Sashabg1228/dread/documentation/documentation/images/robot-close.JPG

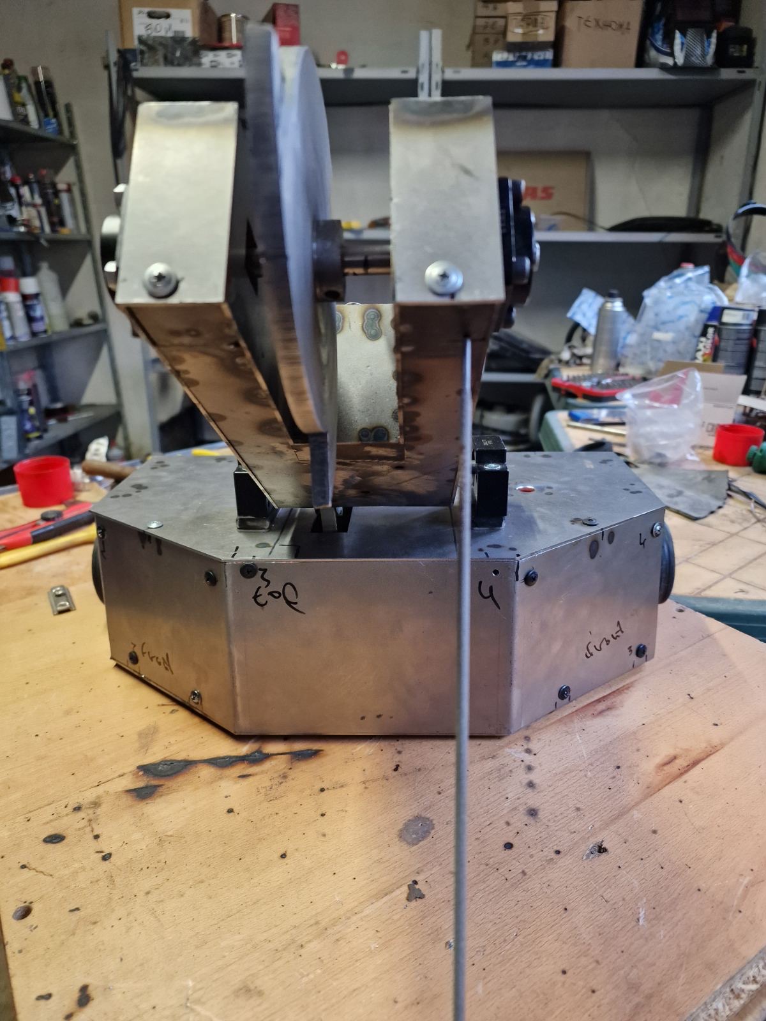
documentation/documentation/images/robot-close.JPG
