Sashabg1228/dread/documentation/documentation/images/robot-high.JPG

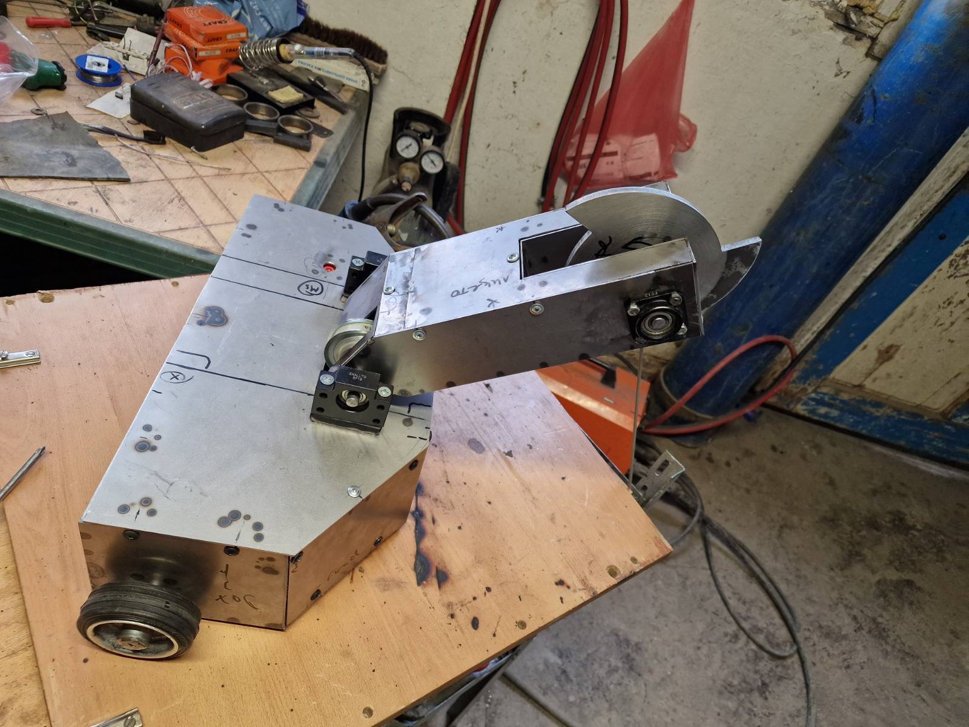
documentation/documentation/images/robot-high.JPG
