Sashabg1228/dread/documentation/documentation/images/robot-strange.JPG

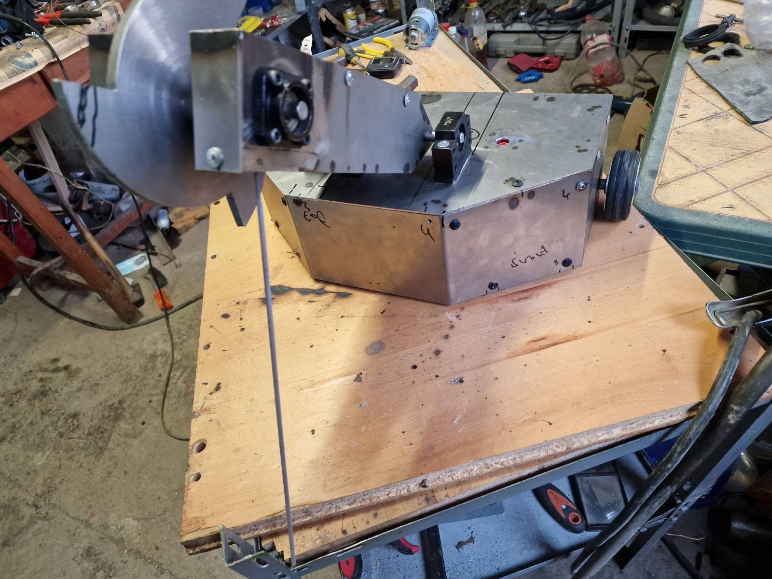
documentation/documentation/images/robot-strange.JPG
