Sashabg1228/dread/documentation/documentation/images/using-legs.png

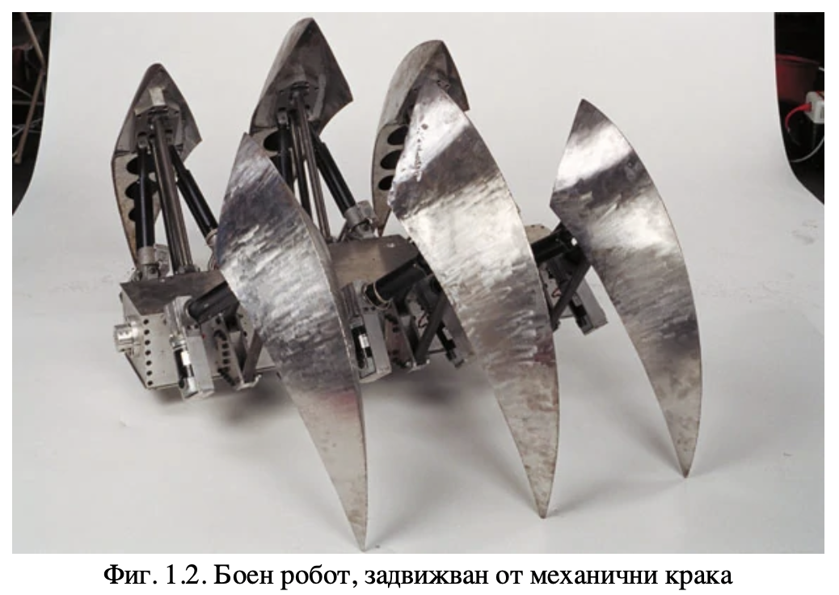
documentation/documentation/images/using-legs.png
