Sashabg1228/dread/documentation/documentation/images/wireless-comparison.png

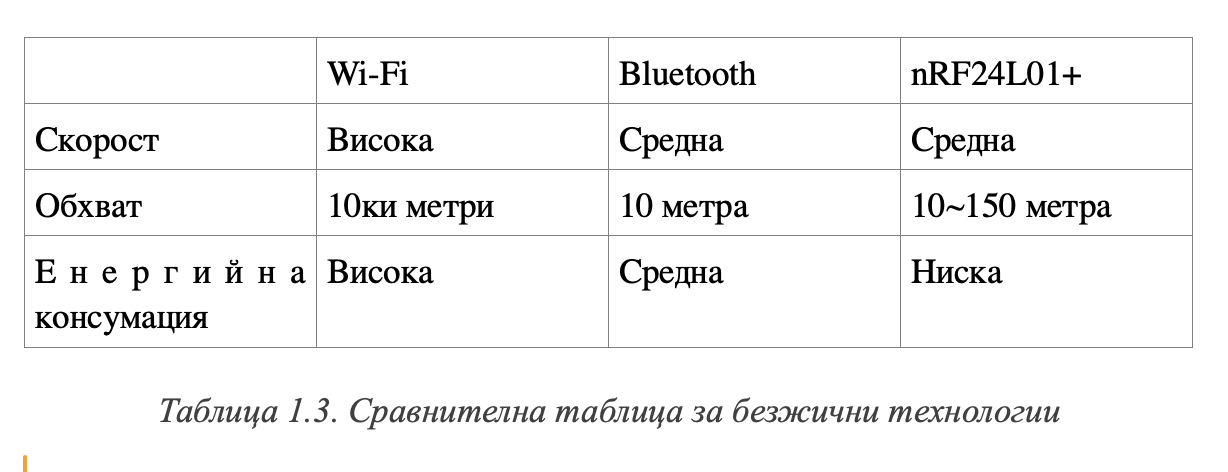
documentation/documentation/images/wireless-comparison.png
