Sashabg1228/dread/photos/IMG_7836.jpg

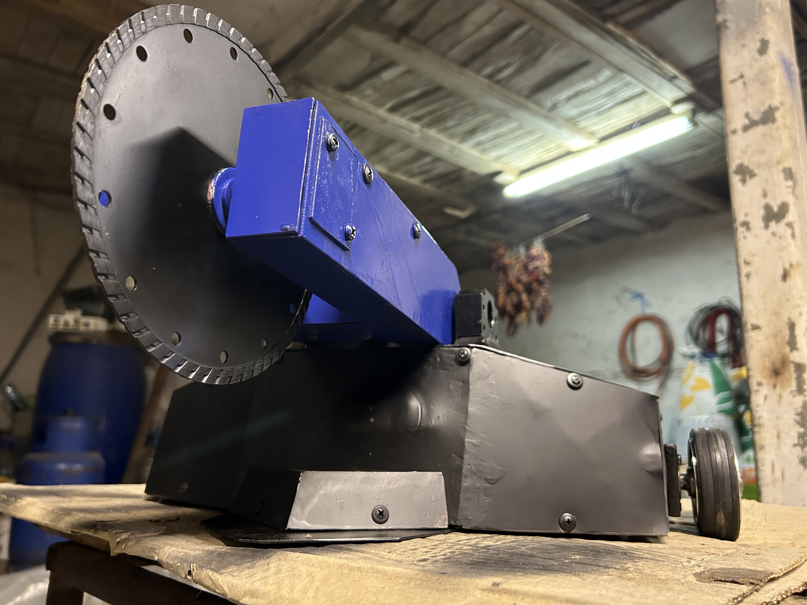
photos/IMG_7836.jpg
