Sashabg1228/dread/photos/IMG_7838.jpg

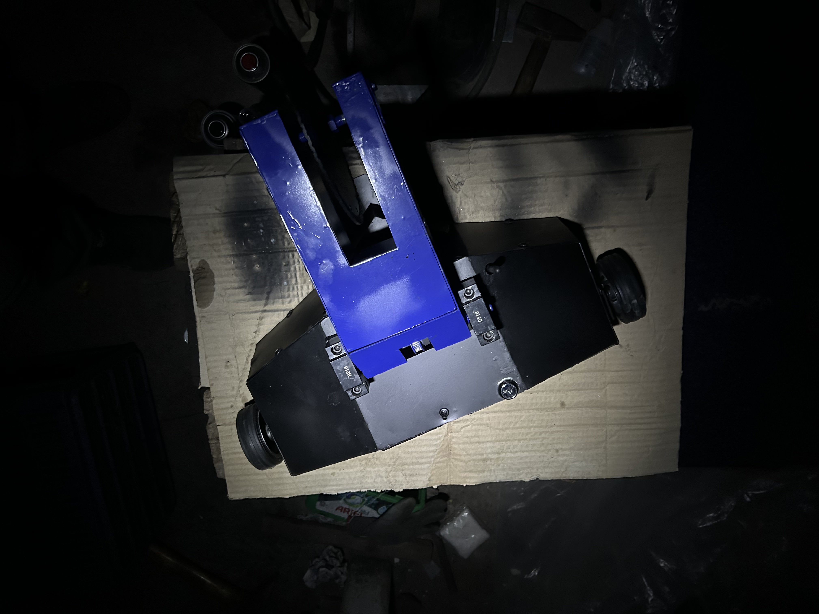
photos/IMG_7838.jpg
