Sashabg1228/dread/photos/IMG_7841.jpg

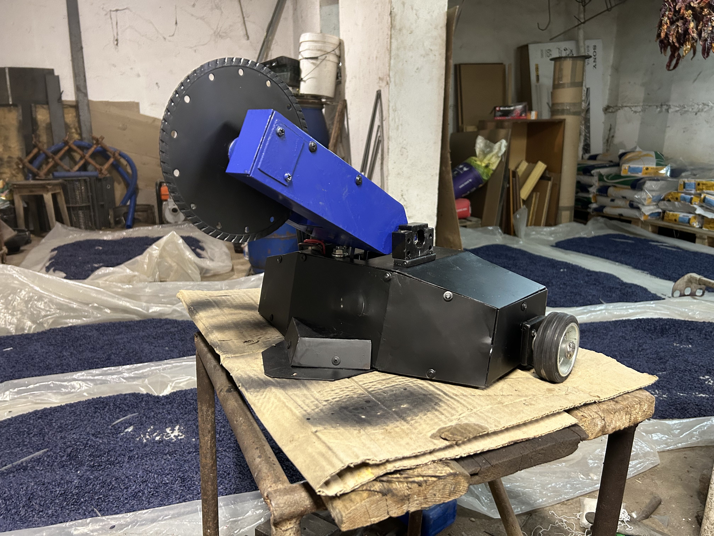
photos/IMG_7841.jpg
