Sashabg1228/dread/materials/blockShemaRobot.png

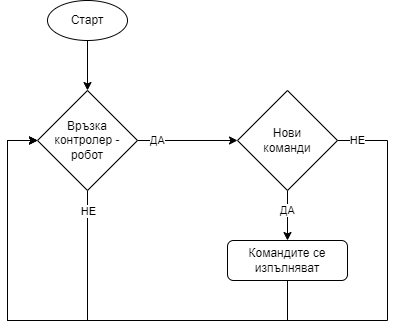
materials/blockShemaRobot.png
