Sashabg1228/dread/materials/blokShemaDistancionno.png

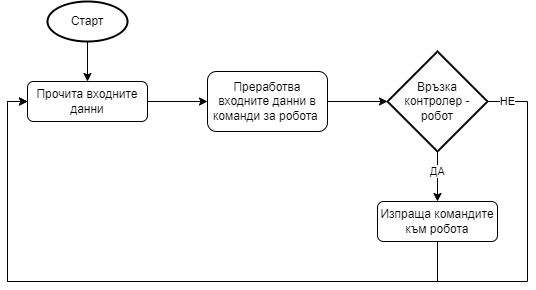
materials/blokShemaDistancionno.png
