Sashabg1228/dread/3d model/for cutting/hand/hand outer wall.dxf

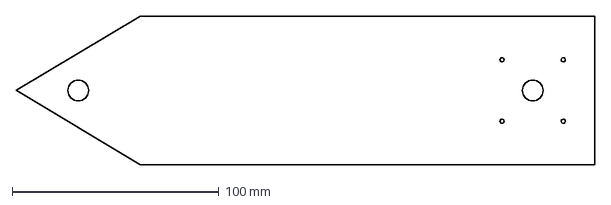
[picture p81: CAD file, 2023-12-17]
3d model/for cutting/hand/hand outer wall.dxf
280.0 x 72.0 mm
