Sashabg1228/dread/3d model/for cutting/body/body back.dxf

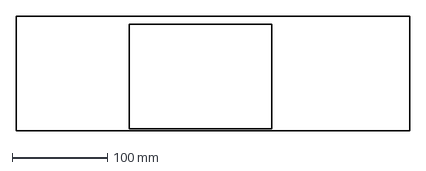
[picture p82: CAD file, 2023-12-17]
3d model/for cutting/body/body back.dxf
414.0 x 120.0 mm
