Sashabg1228/dread/3d model/for cutting/hand/hand outer wall front.dxf

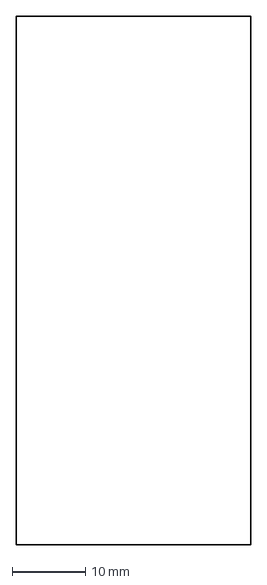
[picture p83: CAD file, 2023-12-17]
3d model/for cutting/hand/hand outer wall front.dxf
32.0 x 72.0 mm
