Sashabg1228/dread/3d model/for cutting/body/body bottom.dxf

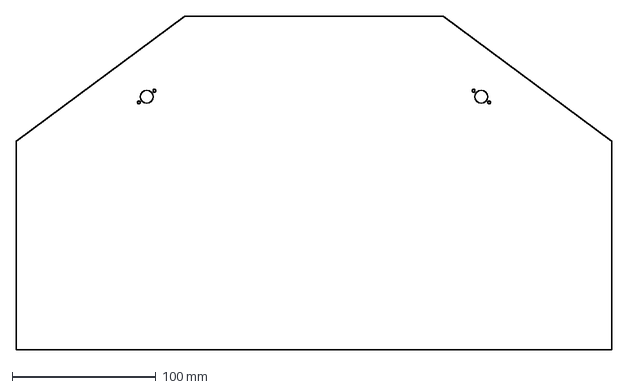
[picture p84: CAD file, 2023-12-17]
3d model/for cutting/body/body bottom.dxf
414.0 x 232.0 mm
