Sashabg1228/dread/3d model/for cutting/body/body inner front level.dxf

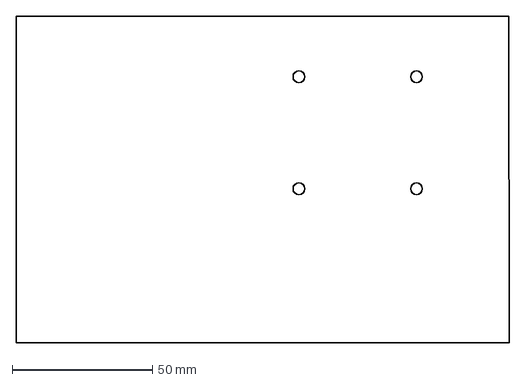
[picture p85: CAD file, 2023-12-17]
3d model/for cutting/body/body inner front level.dxf
176.0 x 116.6 mm
