Sashabg1228/dread/3d model/for cutting/body/body inner wall.dxf

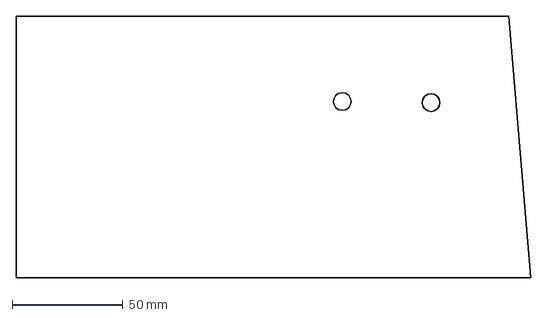
[picture p86: CAD file, 2023-12-17]
3d model/for cutting/body/body inner wall.dxf
232.0 x 118.0 mm
