Sashabg1228/dread/schemas/controller/PCB/PCB_layout.pdf

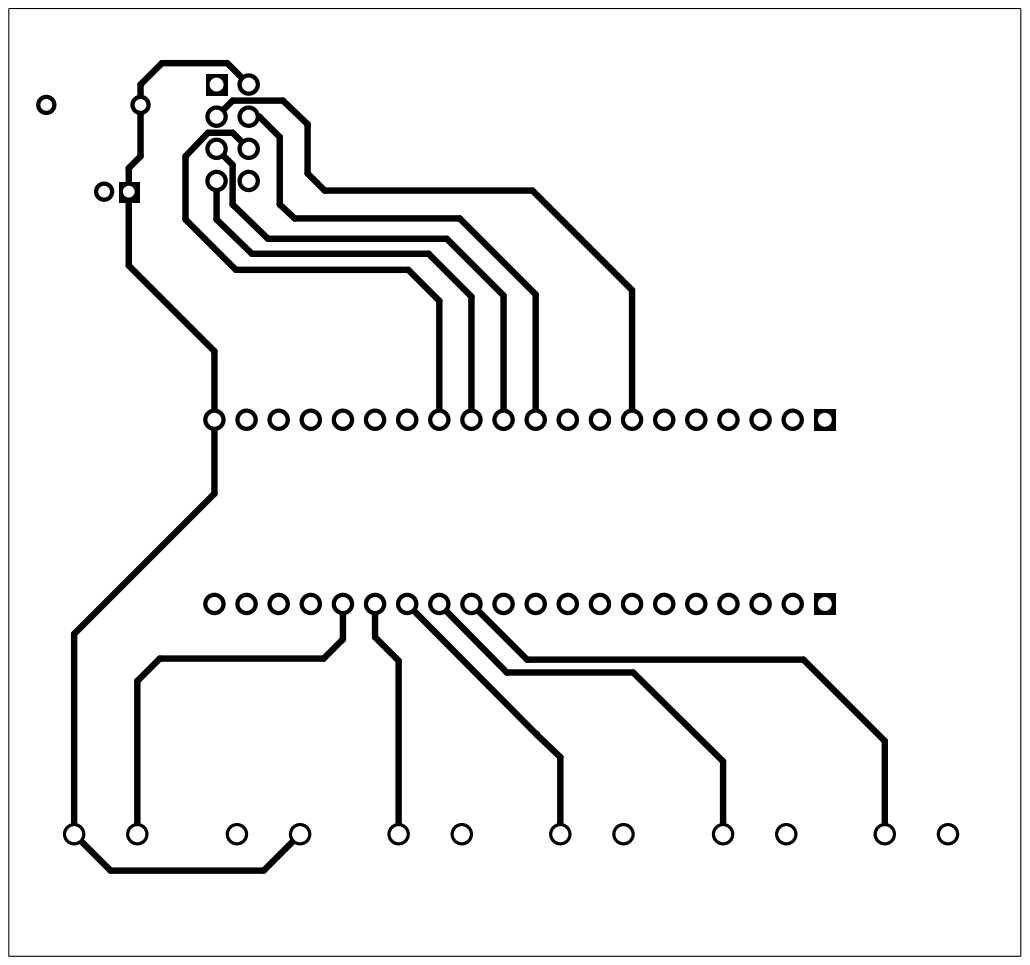
[picture p116: page 1]

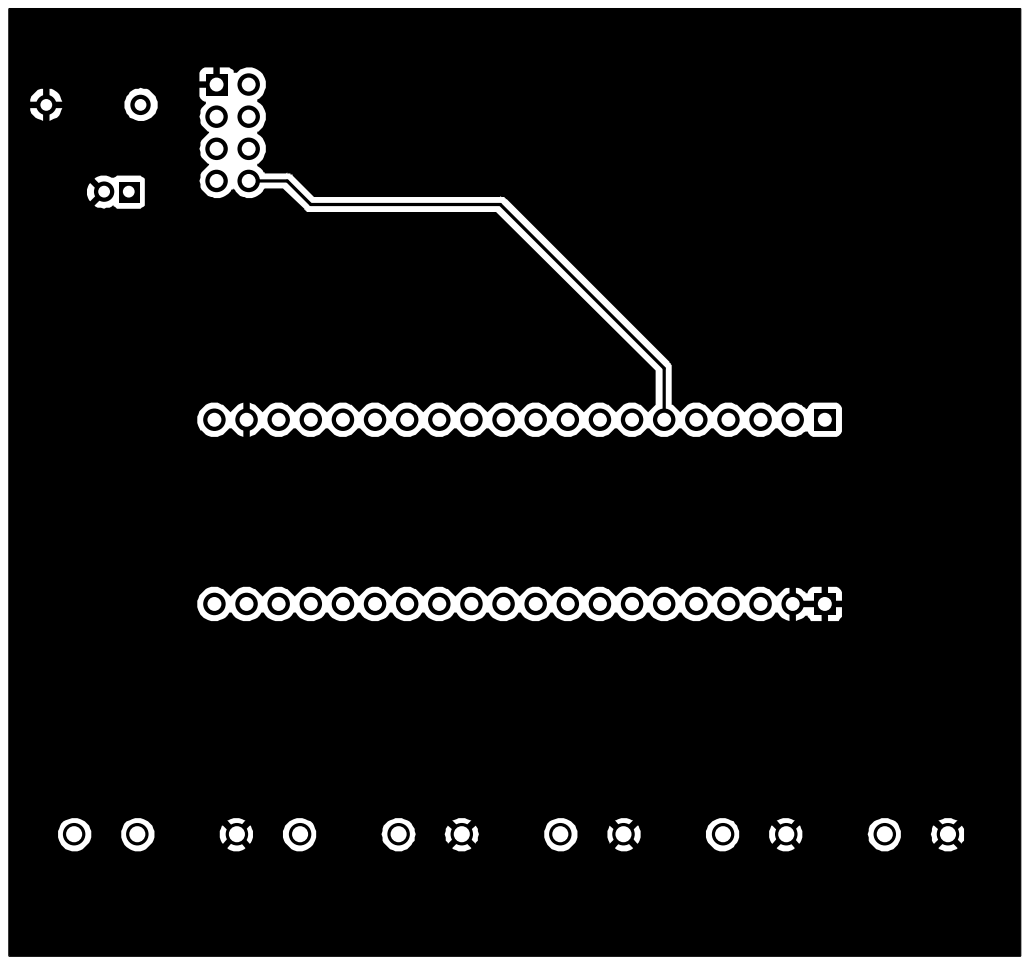
[picture p117: page 2]

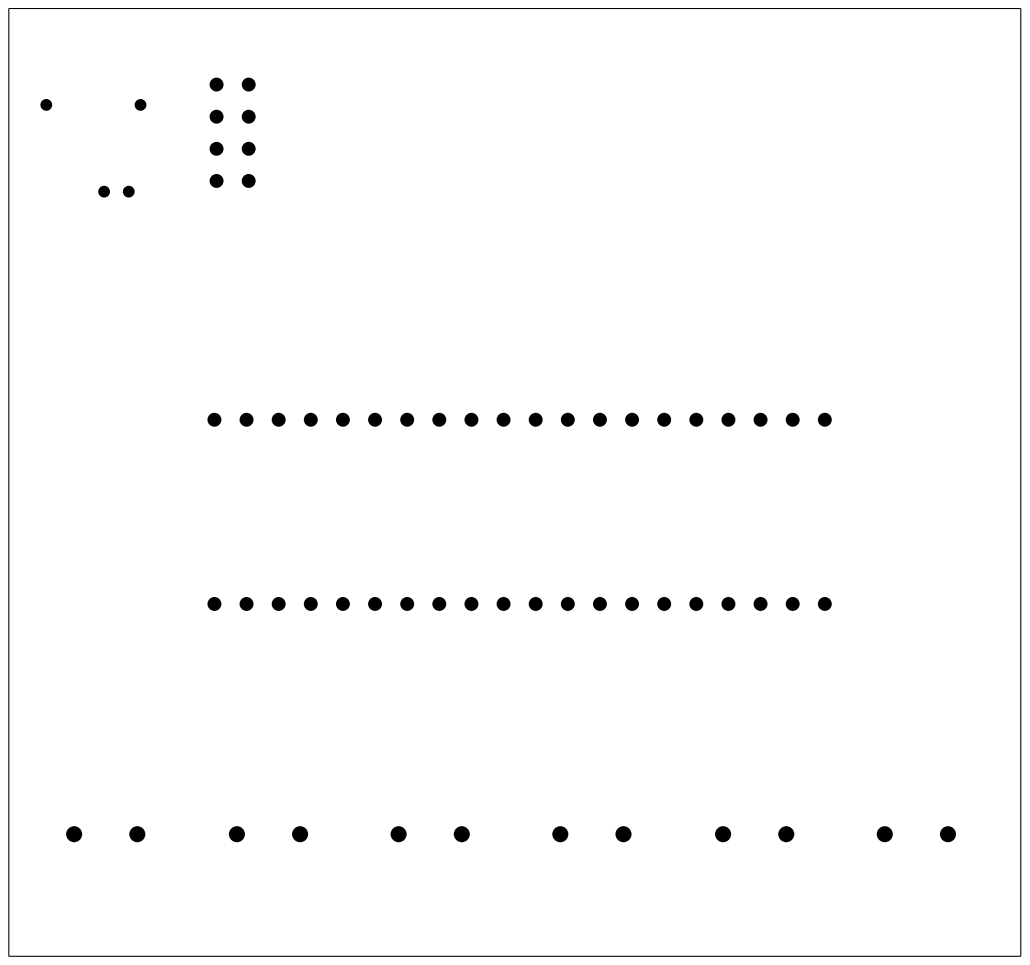
[picture p118: page 3]
