Sashabg1228/dread/schemas/robot/mounting_scheme/robot_mounting_schema.pdf

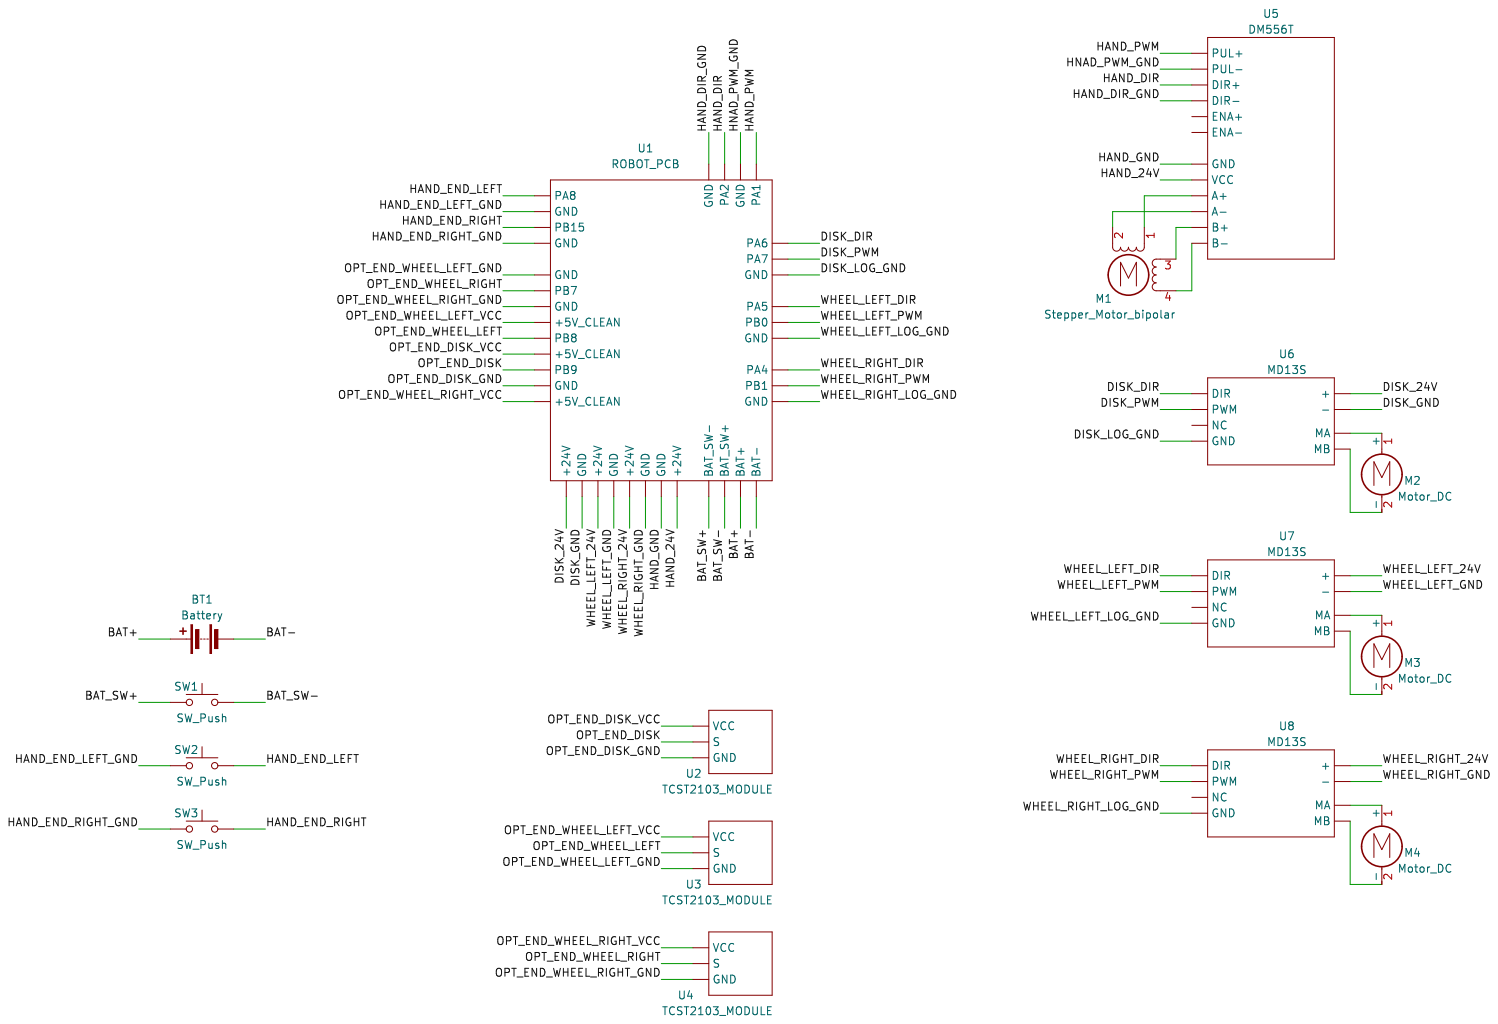
[picture p119: page 1]
