Sashabg1228/dread/3d model/for cutting/body/body front.pdf

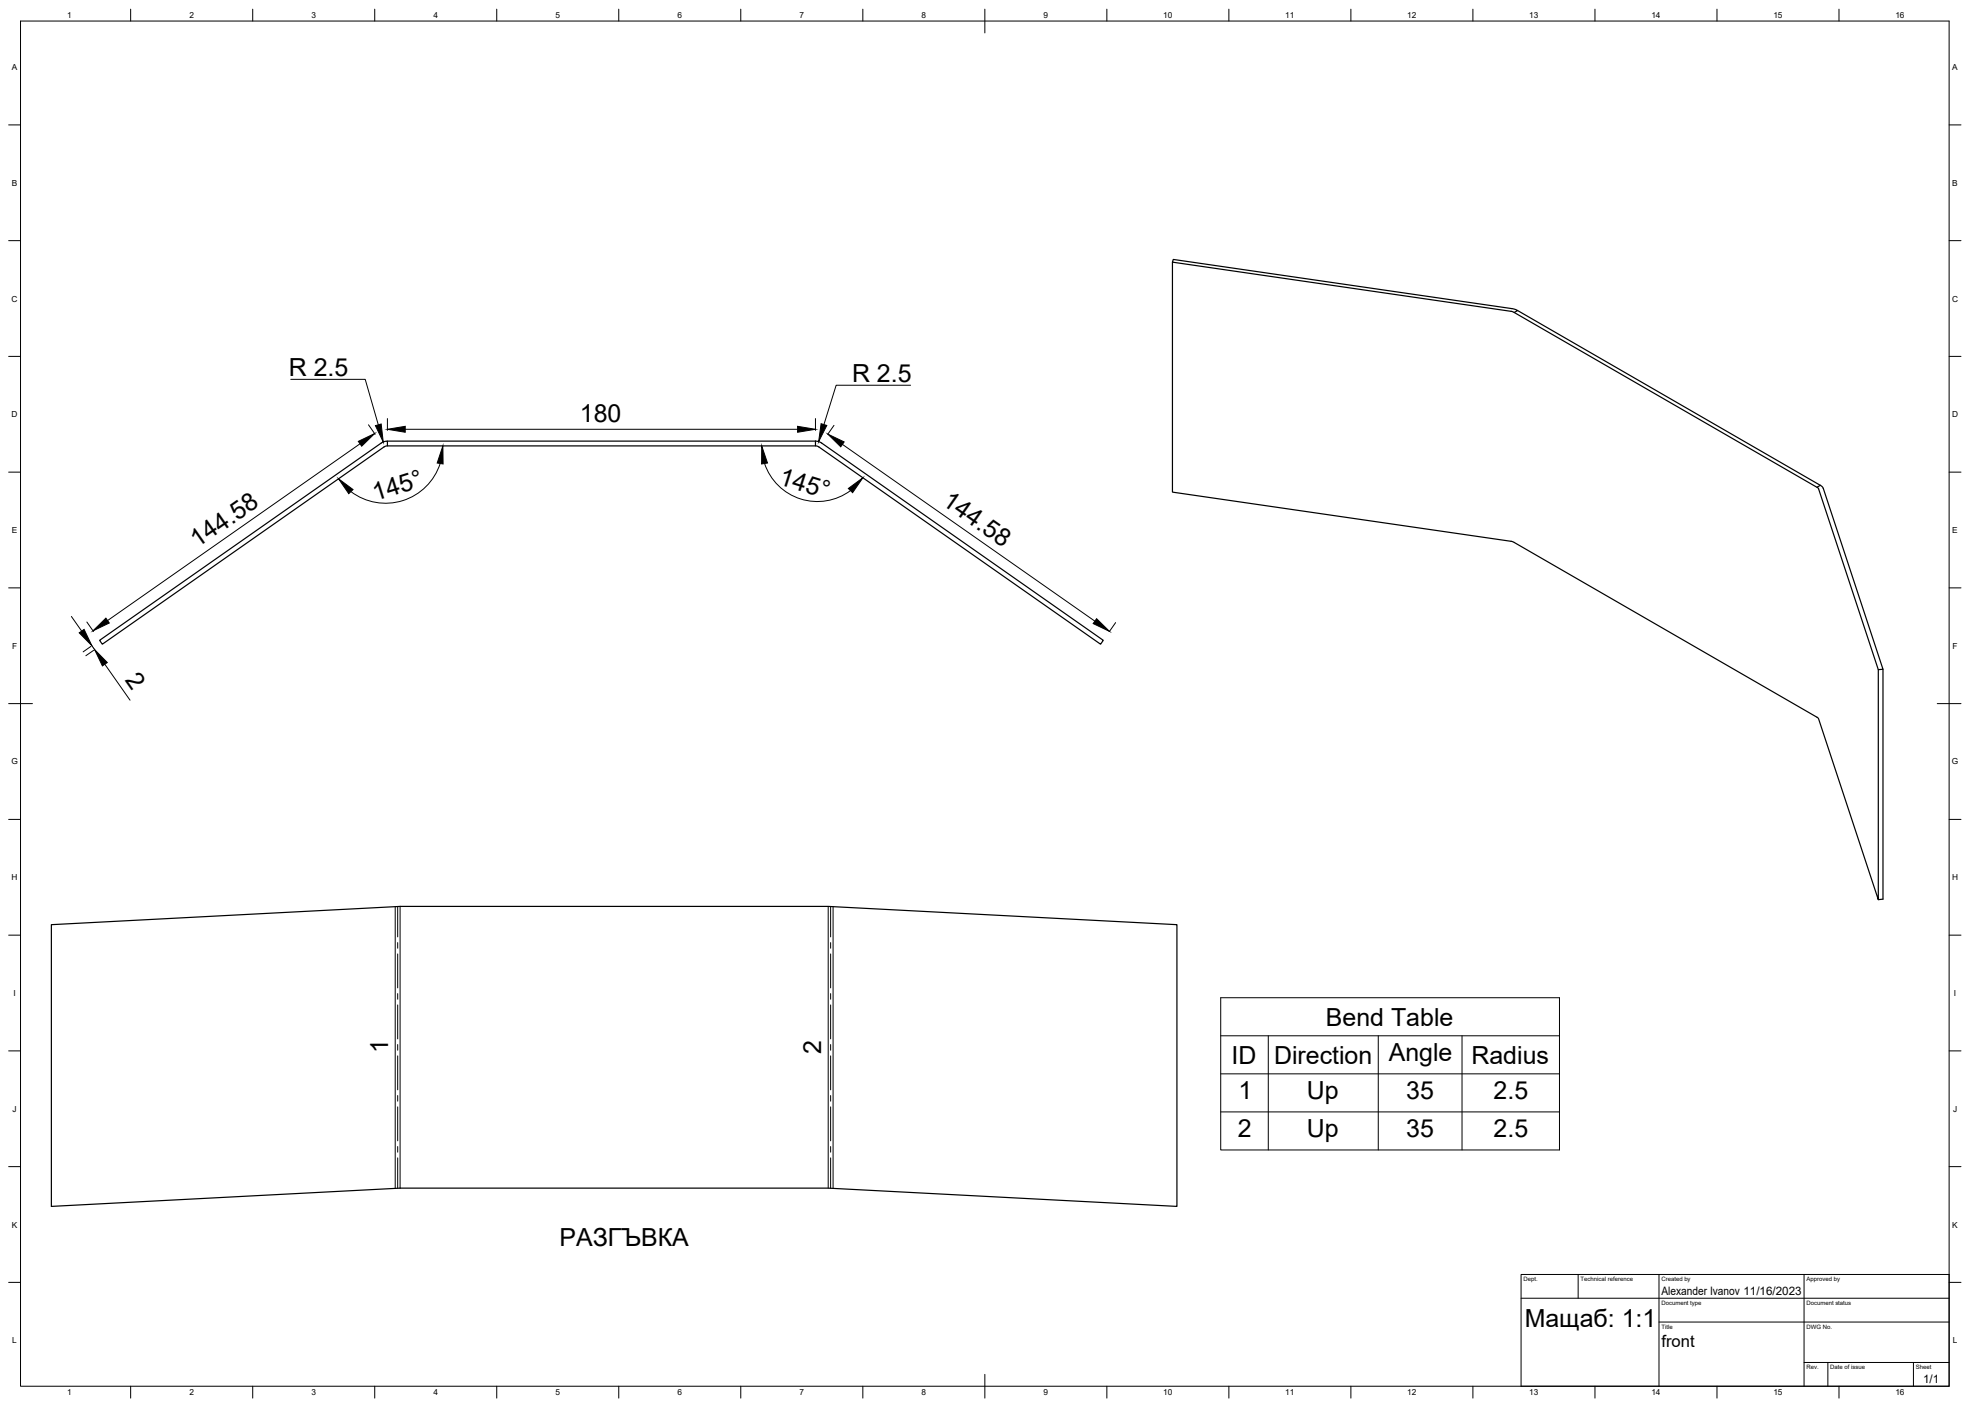
[picture p120: page 1]
Bend Table

ID | Direction | Angle | Radius
1 | Up | 35 | 2.5
2 | Up | 35 | 2.5

Dept. | Technical reference | Created by Alexander Ivanov 11/16/2023 | Approved by

Мащаб: 1:1 | | Document type | Document status

Title front | DWG No.

Rev. | Date of issue | Sheet 1/1
